SpyCrabIndustries/DCC-light-flasher/schematic/schmatic.jpeg

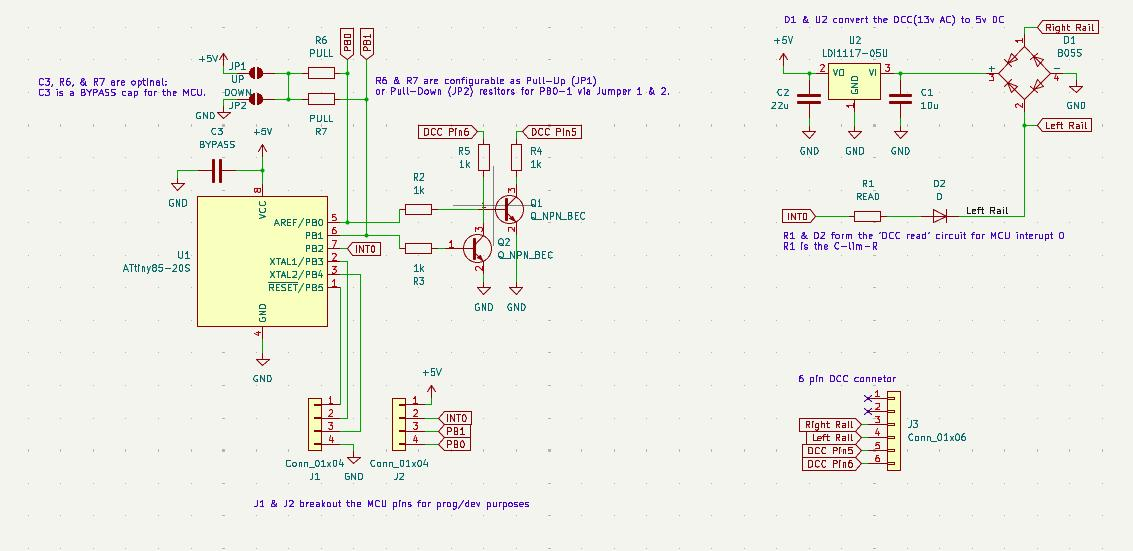
schematic/schmatic.jpeg
